marianop9/reflective-color-sensor/docs/tp_integrador_2025/presentacion/beamer.pdf

## Desarrollo de un Sensor de Colores por Reflexión

Técnicas Digitales III

Federico Beck Mariano Perez

Departamento de Ingeniería Electrónica Facultad Regional San Francisco — UTN

8 de Abril, 2026

Beck, Perez (UTN FRSF) | Sensor de Colores | 8 de Abril, 2026 | 1 / 30

## Contenidos

1 | Introducción
2 | Hardware y Diseño
3 | Circuito de Acondicionamiento
4 | Caracterización del LDR
5 | Proceso de Medición
6 | Resultados
7 | Firmware
8 | Comparación y Conclusiones
Beck, Perez (UTN FRSF) | Sensor de Colores | 8 de Abril, 2026 | 2 / 30

## Introducción y Motivación

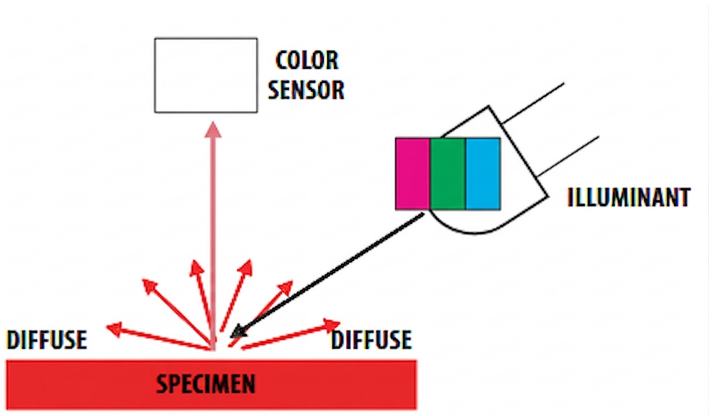
[picture p31: figure]

Objetivo: Dispositivo de bajo costo para determinación de color. Principio: Reflexión de luz roja, verde y azul sobre una superficie. Sensor: Resistencia dependiente de la luz (LDR).

Beck, Perez (UTN FRSF) | Sensor de Colores | 8 de Abril, 2026 | 3 / 30

## Opciones Comerciales

Sensor Adafruit TCS34725: utiliza luz blanca, filtros, y un fotodiodo.

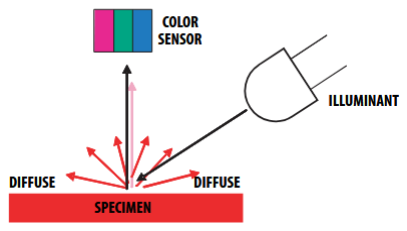
[picture p32: figure]

Figura: Sensor Adafruit TCS34725.

Beck, Perez (UTN FRSF) | Sensor de Colores | 8 de Abril, 2026 | 4 / 30

## Arquitectura del Dispositivo

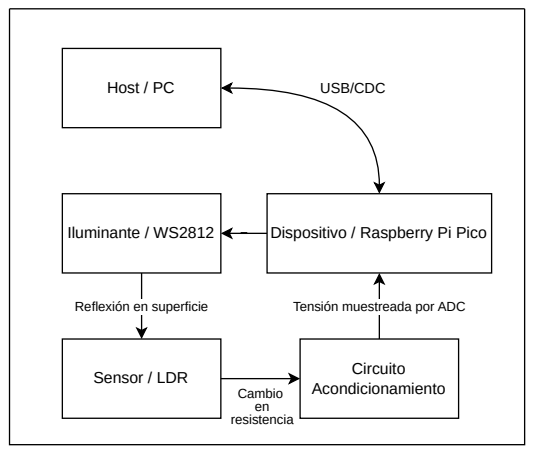
[picture p33: figure]
Host / PC; USB/CDC; Dispositivo / Raspberry Pi Pico; Reflexión en superficie; Iluminante / WS2812; Sensor / LDR; Tensión muestreada por ADC; Circuito; Cambio; Acondicionamiento; en resistencia

Beck, Perez (UTN FRSF) | Sensor de Colores | 8 de Abril, 2026 | 5 / 30

## Diseño Físico y Carcasa

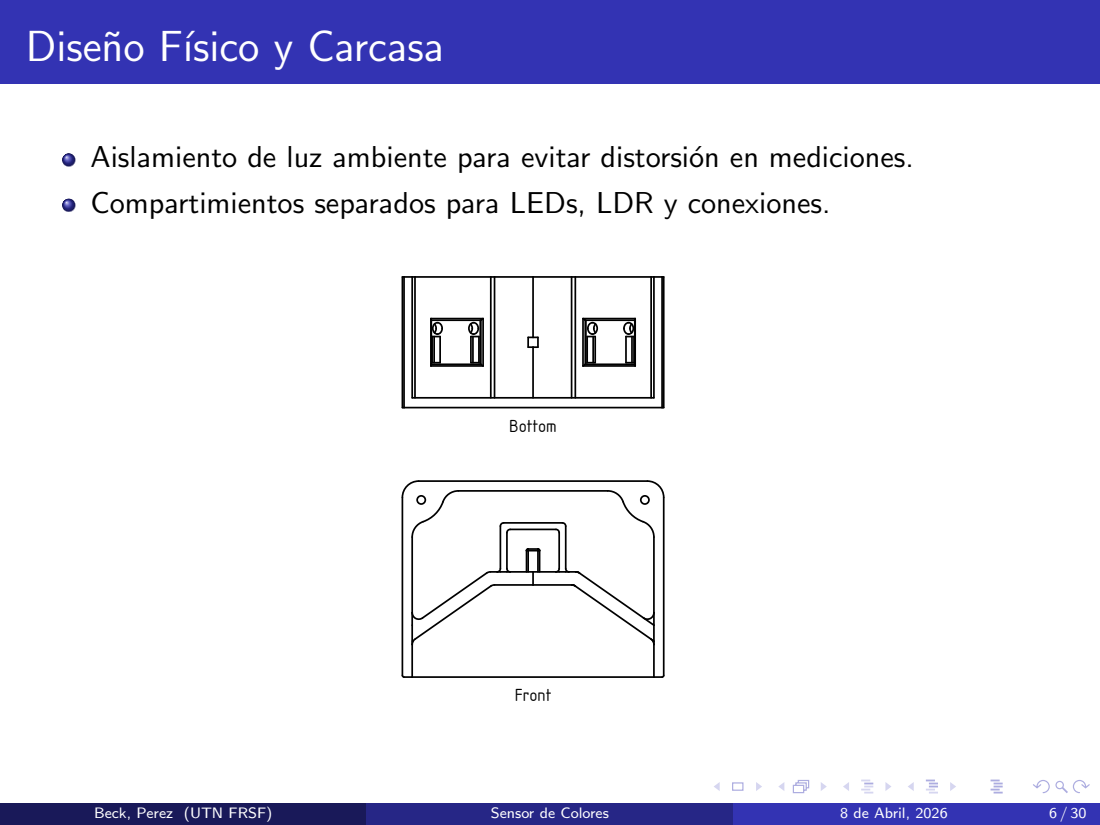
[picture p34: page 6]
Front; Bottom; Beck, Perez (UTN FRSF); Sensor de Colores; 8 de Abril, 2026

Aislamiento de luz ambiente para evitar distorsión en mediciones.
Compartimientos separados para LEDs, LDR y conexiones.

## Componentes Electrónicos: LDR


Respuesta no lineal
Distintas sensibilidades a distintas longitudes de onda.
Baja trazabilidad
Respuesta variable
La respuesta se puede aproximar como:

R = KaE

−γ

Beck, Perez (UTN FRSF) | Sensor de Colores | 8 de Abril, 2026 | 7 / 30

## Componentes Electrónicos

Unidad de Control — Raspberry Pi Pico: Microcontrolador RP2040
DMA para muestreo de ADC
Stack USB
I/O programable
Iluminantes:
LEDs WS2812 (RGB)
Múltiples LEDs conectados en cascada Circuito de Acondicionamiento: Amplificador operacional LM358 Switch cuádruple CD4066
Resistencias de 1 kΩ, 10 kΩ y 100 kΩ

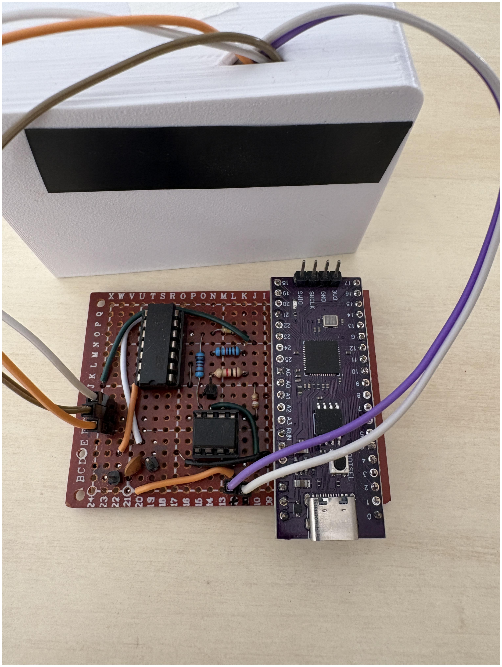
[picture p35: figure]

Beck, Perez (UTN FRSF) | Sensor de Colores | 8 de Abril, 2026 | 8 / 30

## Acondicionamiento de Señal


Vo = V+ + (V+ − Vs )

Rf

RLDR
Vo = V+ + (V+ − Vs )Rf G

Mediante el CD4066, Rf puede tomar distintos valores discretos para evitar la saturación ante el amplio rango del LDR (1 kΩ a 1000 kΩ).

Beck, Perez (UTN FRSF) | Sensor de Colores | 8 de Abril, 2026 | 9 / 30

## Respuesta del Circuito

G =

V+ − Vo
Rf ∗ (Vs − V+)


Figura: Tensión de salida vs Resistencia del LDR | para distintas Rf .
Beck, Perez (UTN FRSF) | Sensor de Colores | 8 de Abril, 2026 | 10 / 30

## Modelo Matemático del LDR

La respuesta del LDR no es lineal:

R = KE ⁻γ

E: Iluminancia
Ka, γ: Parámetros desconocidos.
Beck, Perez (UTN FRSF) | Sensor de Colores | 8 de Abril, 2026 | 11 / 30

## Modelo Matemático del LDR

La respuesta del LDR no es lineal:

R = KE ⁻γ

E: Iluminancia
Ka, γ: Parámetros desconocidos.

Expresado en terminos de conductancia:

G = KaE

γ

Beck, Perez (UTN FRSF) | Sensor de Colores | 8 de Abril, 2026 | 11 / 30

## Iluminancia

Definición

La iluminancia es la cantidad de flujo luminoso que incide sobre una superficie por unidad de área.
Define qué tan iluminada está una superficie
Medida en lux (1 lux = 1 lm/m²
)
Disminuye con el cuadrado de la distancia a la fuente Se mide con un luxómetro
Beck, Perez (UTN FRSF) | Sensor de Colores | 8 de Abril, 2026 | 12 / 30

## Modelo Matemático Aproximado del LDR


Es imposible determinar la iluminancia, por lo que se utiliza una aproximación.

E ≈ c, c ∈ [0, 255]

G = Kac

| γ
Beck, Perez (UTN FRSF) | Sensor de Colores | 8 de Abril, 2026 | 13 / 30

## Región de Funcionamiento

Se define una región de funcionamiento del dispositivo.
Para muestras del ADC con códigos por debajo de 850 y por encima de 3800, la respuesta del circuito no variaba al cambiar la intensidad de los LED.


Beck, Perez (UTN FRSF) | Sensor de Colores | 8 de Abril, 2026 | 14 / 30

## Proceso de Calibración


Cada color por separado
Barrido de intensidad
40 valores de intensidad
Espaciado logarítmico
Si la medición no se encuentra dentro de la región de funcionamiento, se ajusta la resistencia de ganancia y se repite.
Beck, Perez (UTN FRSF) | Sensor de Colores | 8 de Abril, 2026 | 15 / 30

## Proceso de Calibración

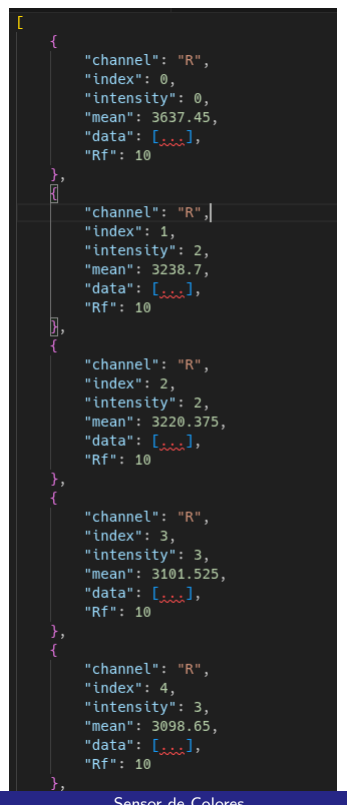
[picture p36: figure]

Beck, Perez (UTN FRSF) | Sensor de Colores | 8 de Abril, 2026 | 16 / 30

## Proceso de Calibración


Beck, Perez (UTN FRSF) | Sensor de Colores | 8 de Abril, 2026 | 16 / 30

## Cálculo de los Parametros del LDR

Una vez recolectadas las muestras para cada color, se aplica la técnica de mínimos cuadrados (LSQ) para aproximar la respuesta.
La i-ésima muestra recolectada se expresa como:

Gi = Kac

γ
i
Beck, Perez (UTN FRSF) | Sensor de Colores | 8 de Abril, 2026 | 17 / 30

## Cálculo de los Parametros del LDR

Una vez recolectadas las muestras para cada color, se aplica la técnica de mínimos cuadrados (LSQ) para aproximar la respuesta.
La i-ésima muestra recolectada se expresa como:

Gi = Kac

γ
i
ln Gi = lnKa + γ ln c | (1)
Beck, Perez (UTN FRSF) | Sensor de Colores | 8 de Abril, 2026 | 17 / 30

## Cálculo de los Parametros del LDR

Una vez recolectadas las muestras para cada color, se aplica la técnica de mínimos cuadrados (LSQ) para aproximar la respuesta.
La i-ésima muestra recolectada se expresa como:

Gi = Kac

γ
i
ln Gi = lnKa + γ ln c | (1)

Considerando N muestras distintas, se arma un sistema de ecuaciones y se expresa en forma de matrices:

ln G1
ln G2
ln GN

=

1 | ln c1
1 | ln c2
1 ln cN

lnKa
γ
(2)
Beck, Perez (UTN FRSF) | Sensor de Colores | 8 de Abril, 2026 | 17 / 30

## Cálculo de los Parámetros del LDR

Considerando N muestras distintas, se arma un sistema de ecuaciones y se expresa en forma de matrices:

ln G1
ln G2
ln GN

=

1 | ln c1
1 | ln c2

1 ln cN

lnKa
γ

Y = Ax

Los valores de la matriz x que mejor se ajustan a las muestras obtenidas se puede calcular como:
x = (A

T A)

−1
A
T Y | (3)
Beck, Perez (UTN FRSF) | Sensor de Colores | 8 de Abril, 2026 | 18 / 30

## Parámetros del LDR

{
"R": {
"Ka": 0.011508412425650682 , " gamma ": 0.8527065806062964 },
"G": {
"Ka": 0.0032507832523976554 , " gamma ": 0.8597395131749697 },
"B": {
"Ka": 0.0030240133142661603 , " gamma ": 0.8283233614433873 }
}
Beck, Perez (UTN FRSF) | Sensor de Colores | 8 de Abril, 2026 | 19 / 30

## Proceso de Medición

Una vez determinados los parámetros del LDR, se pueden tomar mediciones. Para cada color R-G-B:
1 | Se coloca el dispositivo sobre la superficie a medir.
2 | Iluminación a máxima intensidad.
3 | Muestreo de tensión y cálculo de G.
| G ≈ Kac γ
| G se mide
| Ka, γ se conocen de la calibración
Beck, Perez (UTN FRSF) | Sensor de Colores | 8 de Abril, 2026 | 20 / 30

## Resultados

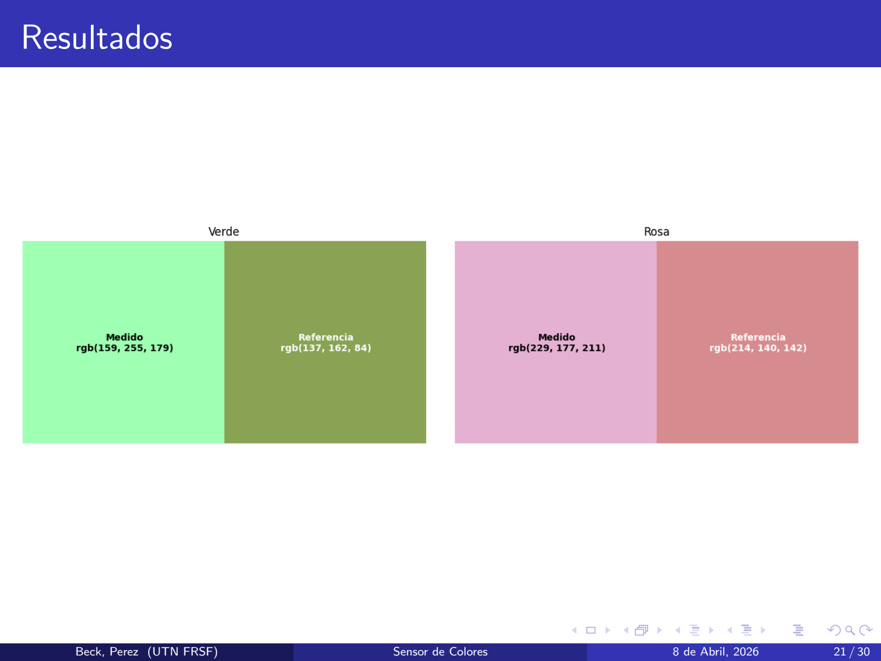
[picture p37: page 25]

Beck, Perez (UTN FRSF) | Sensor de Colores | 8 de Abril, 2026 | 21 / 30

## Resultados

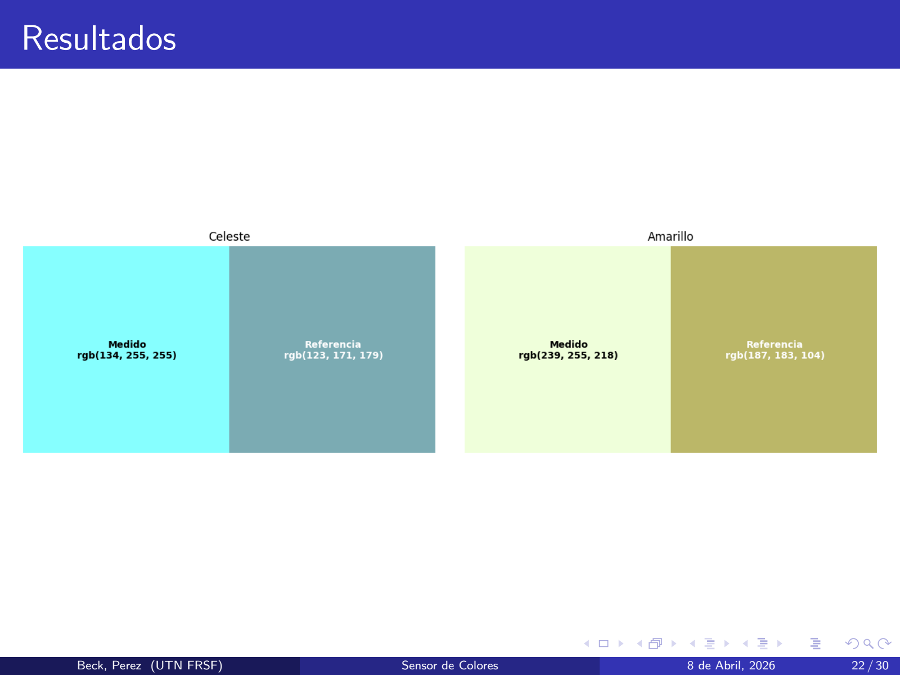
[picture p38: page 26]

Beck, Perez (UTN FRSF) | Sensor de Colores | 8 de Abril, 2026 | 22 / 30

## Implementación en Firmware

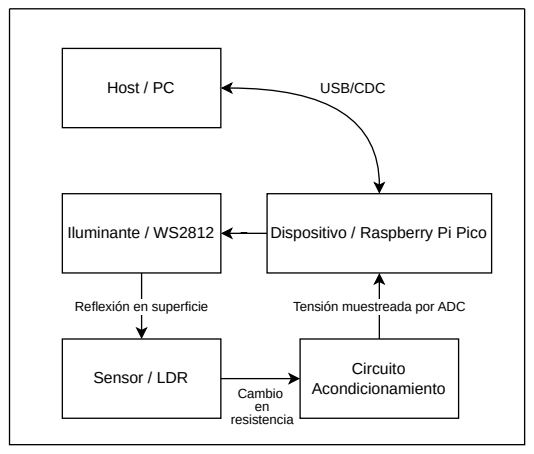
[picture p39: figure]
Host / PC; USB/CDC; Dispositivo / Raspberry Pi Pico; Reflexión en superficie; Iluminante / WS2812; Sensor / LDR; Tensión muestreada por ADC; Circuito; Cambio; Acondicionamiento; en resistencia

Beck, Perez (UTN FRSF) | Sensor de Colores | 8 de Abril, 2026 | 23 / 30

## Arquitectura del Firmware

Implementación en C
Abstracción de hardware: Pico-SDK Implementación del stack USB: TinyUSB SO de tiempo real: FreeRTOS
Beck, Perez (UTN FRSF) | Sensor de Colores | 8 de Abril, 2026 | 24 / 30

## Arquitectura del Firmware

usb task()
Ejecuta del stack USB
Recibe/envía de mensajes desde/hacía el host worker task()
Ejecuta de comandos
Interactúa con periféricos a través de drivers Arma de mensajes de respuesta
Librería ascii-communication-protocol (ACP)

Interpreta mensajes recibidos como comandos Codifica mensajes a enviar en el formato de respuesta

Beck, Perez (UTN FRSF) | Sensor de Colores | 8 de Abril, 2026 | 25 / 30

## Arquitectura del Firmware

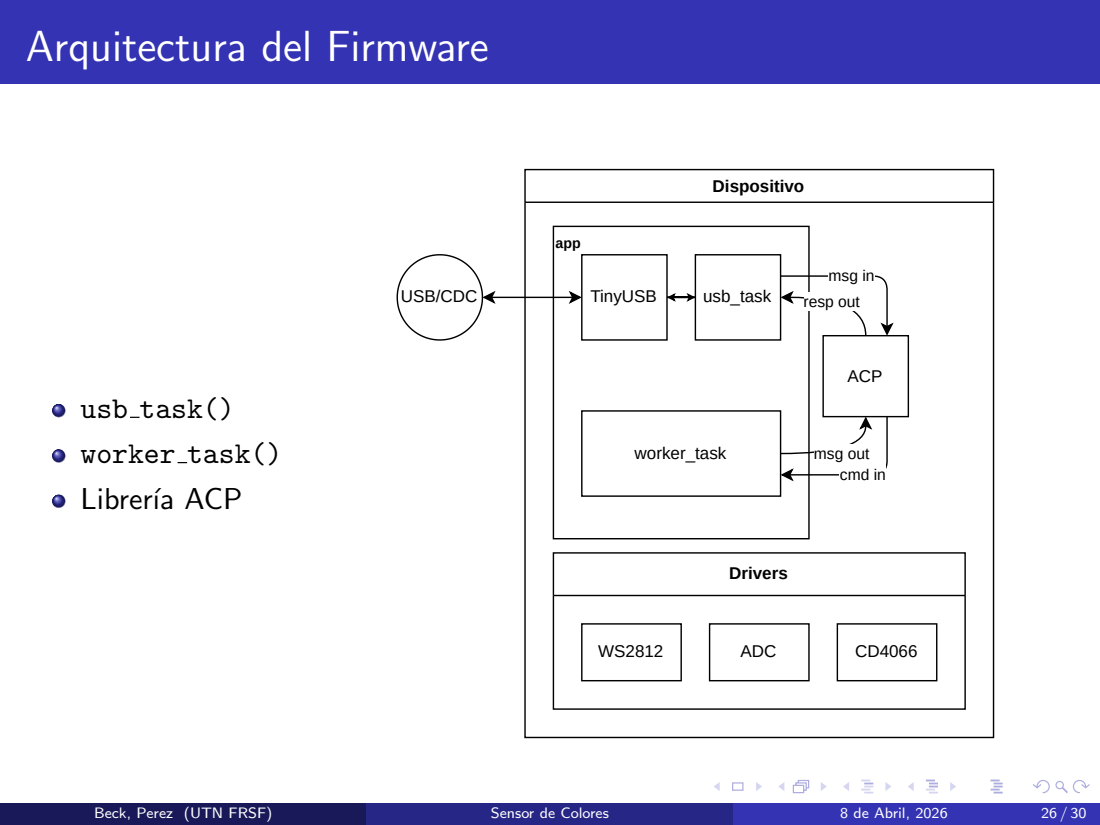
[picture p40: page 30]
Dispositivo; app; msg in; usb_task; worker_task; msg out; cmd in; ACP; Drivers; ADC; resp out USB/CDC; inyUSB; Beck, Perez (UTN FRSF); Sensor de Colores; 8 de Abril, 2026

usb task()
worker task()
Librería ACP

## Aplicación CLI

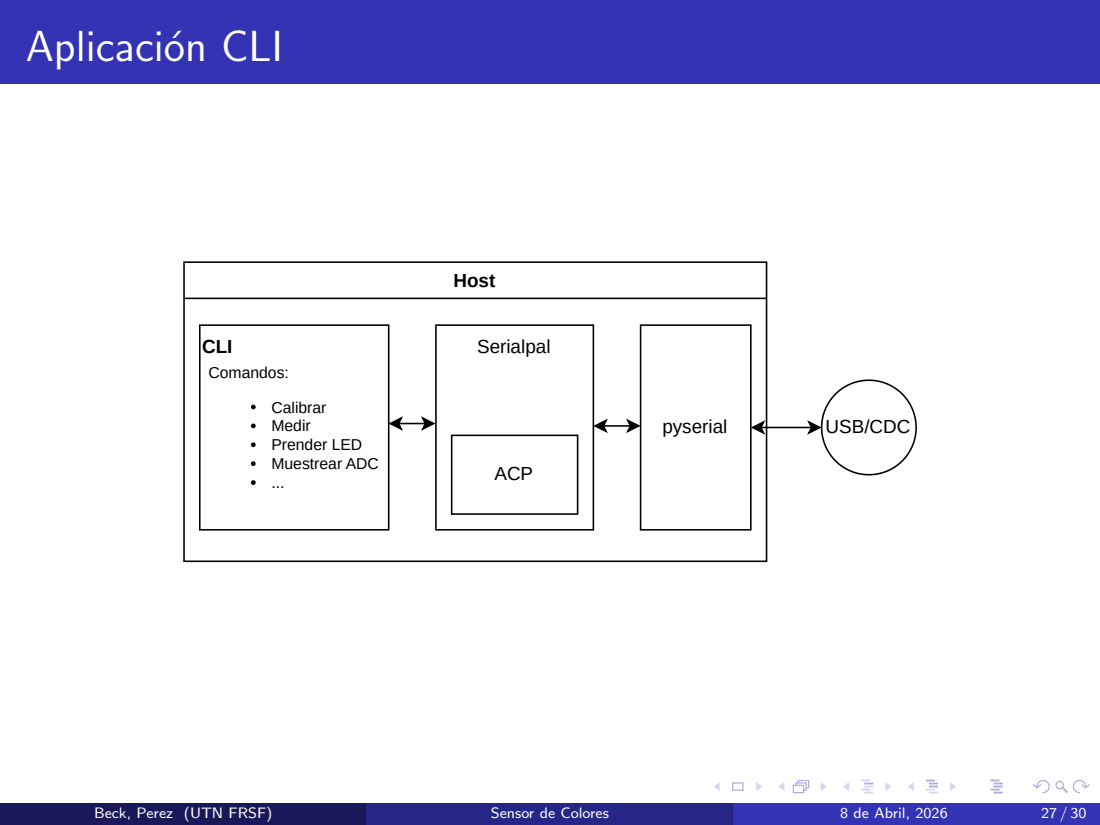
[picture p41: page 31]
Host; pyserial; CLI; Serialpal; Comandos:; ACP; USB/CDC; Beck, Perez (UTN FRSF); Sensor de Colores; 8 de Abril, 2026

Calibrar
Medir
Prender LED Muestrear ADC

## Compración con la Versión Inicial

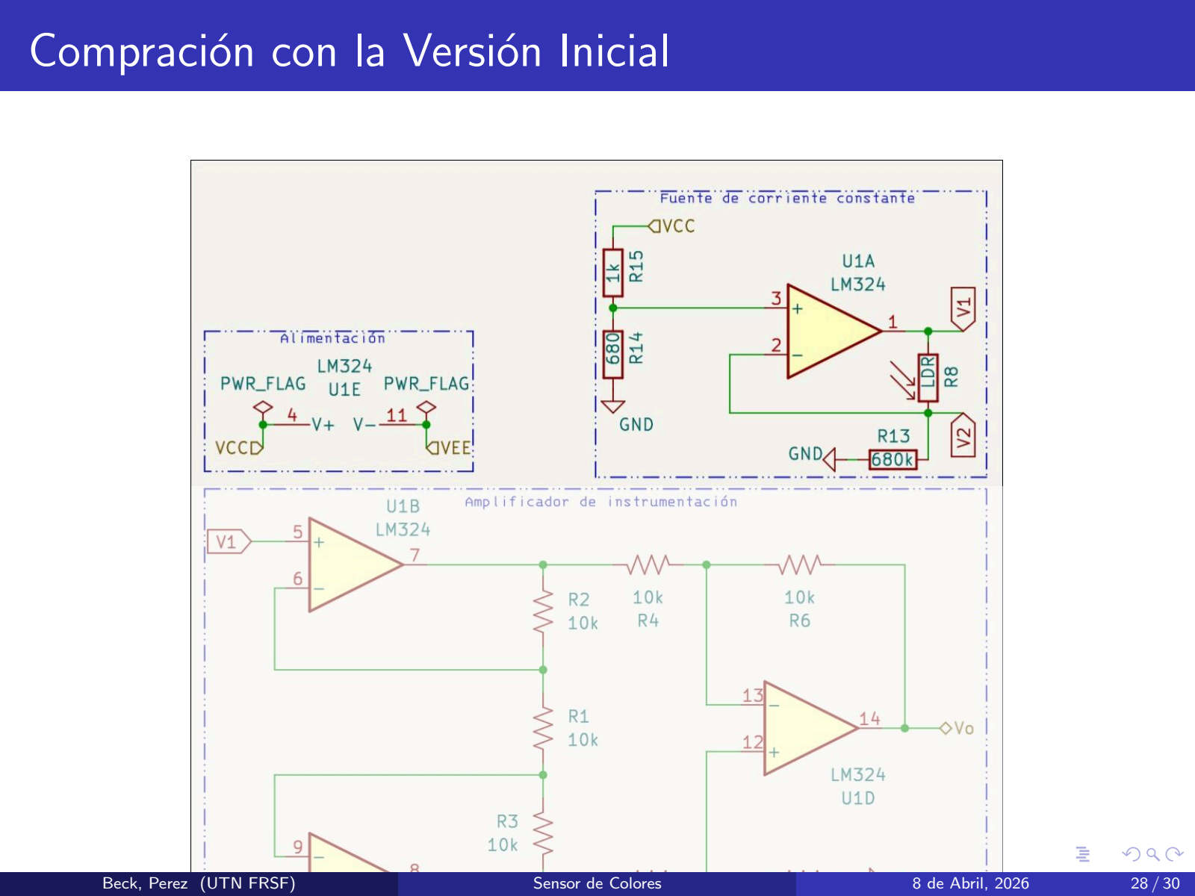
[picture p42: page 32]

Beck, | Perez | (UTN FRSF) | Sensor de Colores | 8 de Abril, 2026 | 28 / 30

## Compración con la Versión Inicial

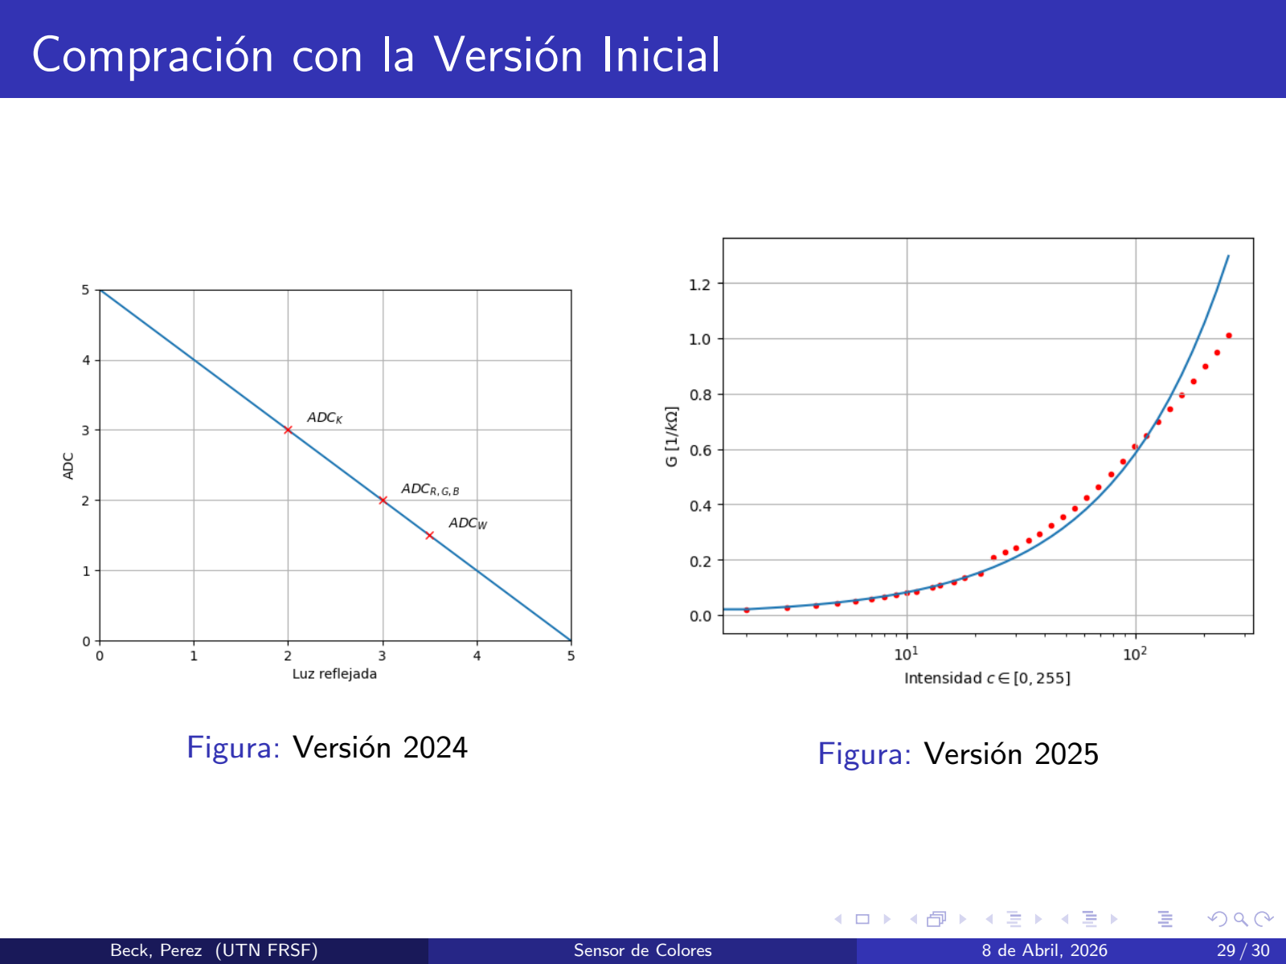
[picture p43: page 33]

Figura: Versión 2024 | Figura: Versión 2025
Beck, Perez (UTN FRSF) | Sensor de Colores | 8 de Abril, 2026 | 29 / 30

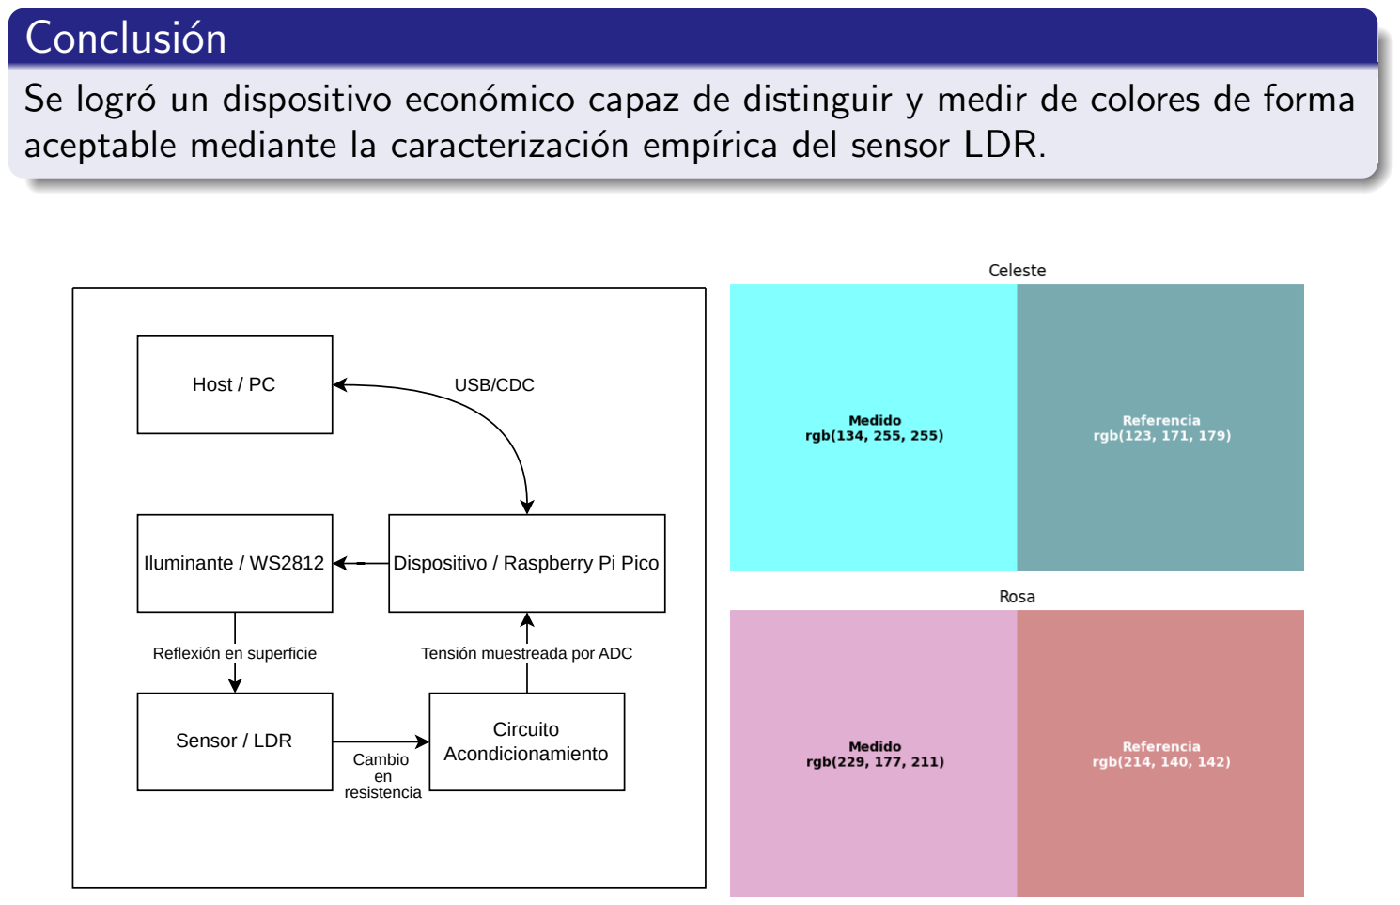
[picture p44: figure]
Conclusión; Dispositivo / Raspberry Pi Pico; Reflexión en superficie; Iluminante / WS2812; Sensor / LDR; Tensión muestreada por ADC; Circuito; Cambio; Acondicionamiento; en resistencia

Se logró un dispositivo económico capaz de distinguir y medir de colores de forma
aceptable mediante la caracterización empírica del sensor LDR. Host / PC | USB/CDC
Beck, Perez (UTN FRSF) | Sensor de Colores | 8 de Abril, 2026 | 30 / 30
