marianop9/reflective-color-sensor/docs/tp_integrador_2025/img/beamer/final_slide.pdf

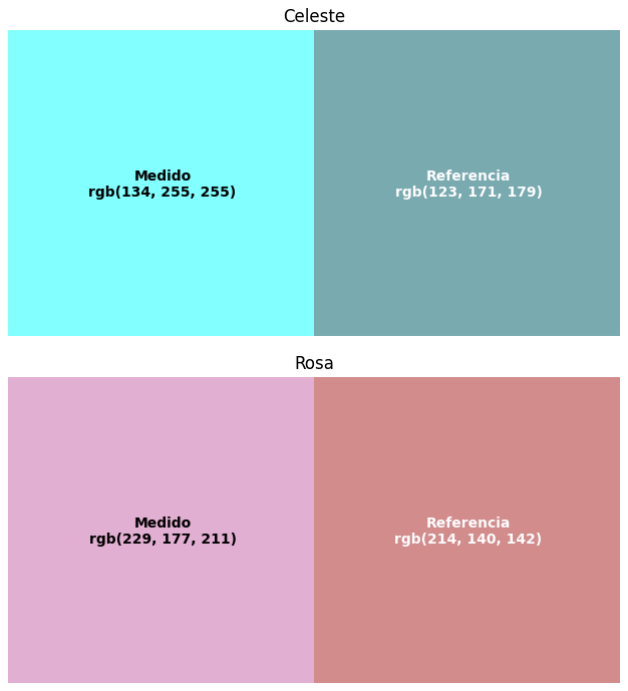
[picture p45: figure]
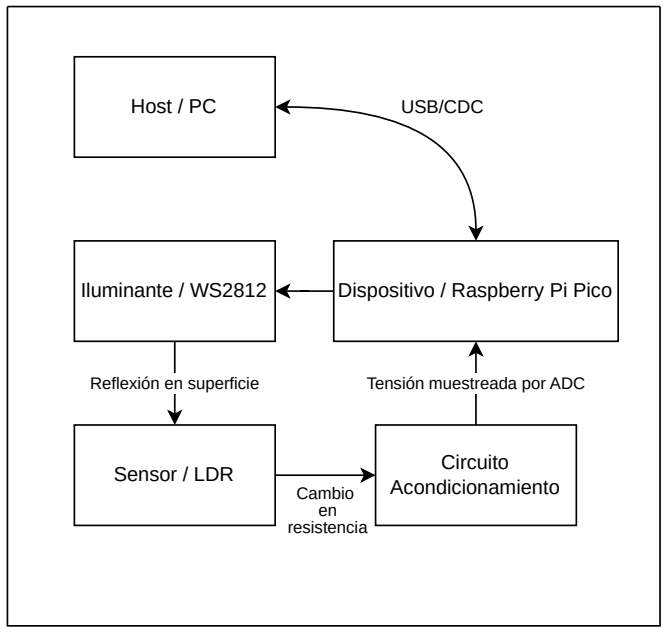
[picture p46: figure]
Host / PC; USB/CDC; Dispositivo / Raspberry Pi Pico; Reflexión en superficie; Iluminante / WS2812; Sensor / LDR; Tensión muestreada por ADC; Circuito; Cambio; Acondicionamiento; en resistencia
