marianop9/reflective-color-sensor/docs/tp_integrador_2025/img/beamer/circuito_2024.pdf

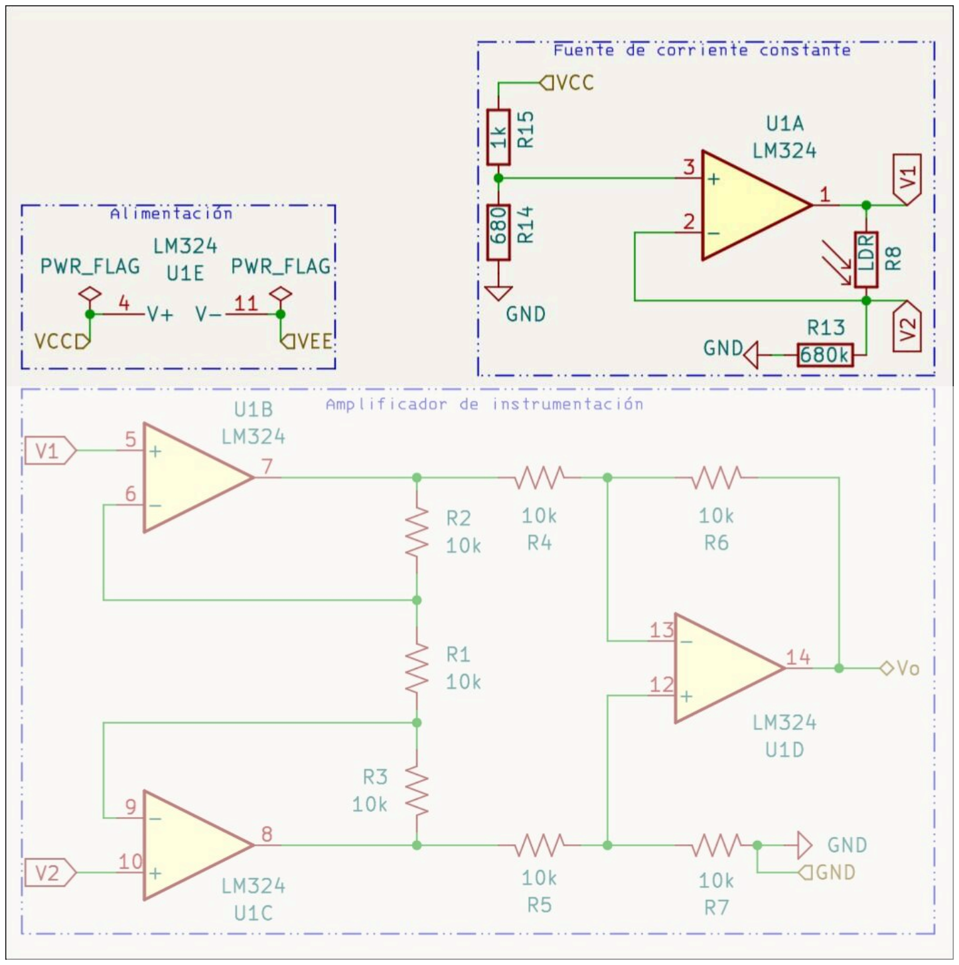
[picture p47: page 1]
