marianop9/reflective-color-sensor/docs/tp_integrador_2025/img/diagrama_inicial.png

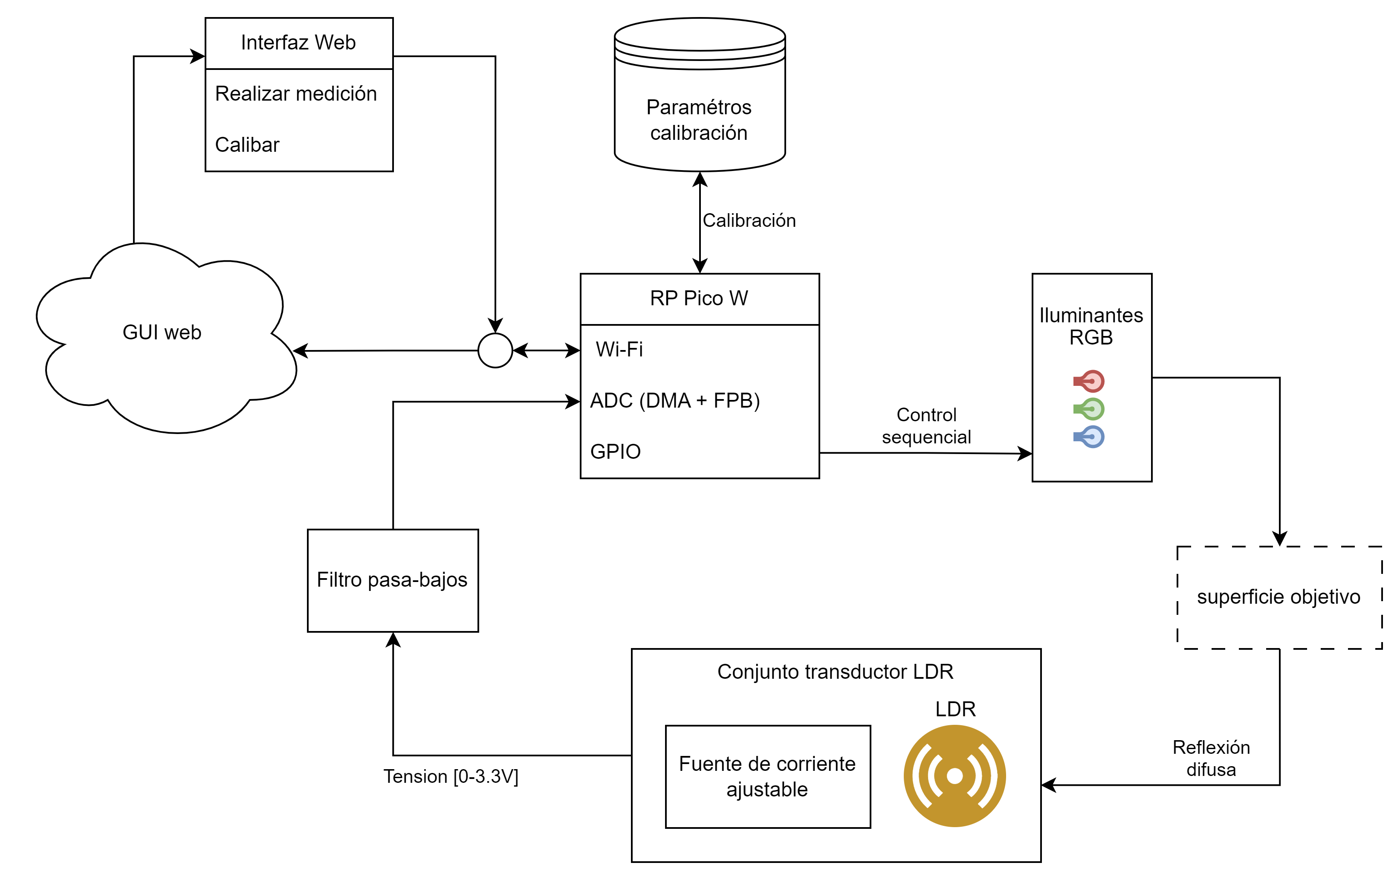
docs/tp_integrador_2025/img/diagrama_inicial.png
