marianop9/reflective-color-sensor/scripts/filtrado_043V.png

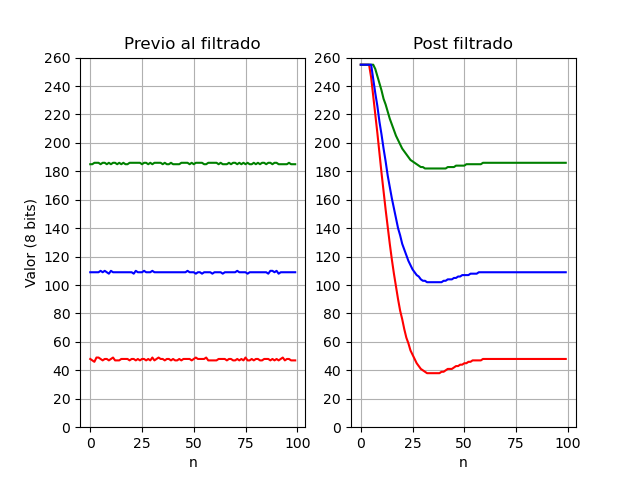
scripts/filtrado_043V.png
