marianop9/reflective-color-sensor/scripts/sin_filtro_043V.png

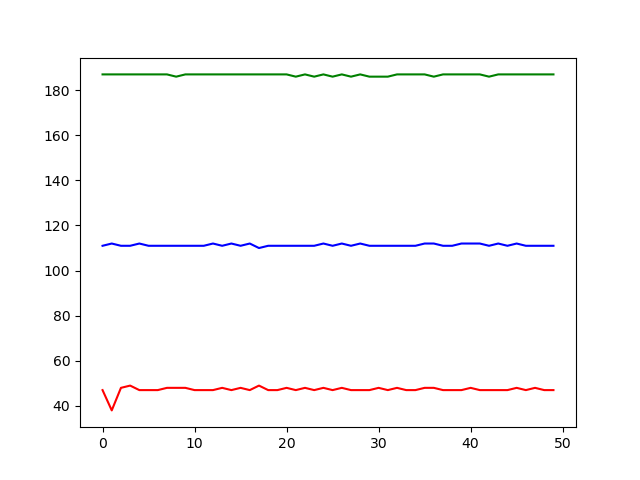
scripts/sin_filtro_043V.png
