marianop9/reflective-color-sensor/circuitos/ldr_conditioning_v2_sim/ldr_conditioning.asc

R1: res; {LDR}
R2: res; {Rf}
R3: res; 1.2k
R4: res; 2.2k
U2: opamp
V1: voltage; 5
Named nets: 0, Vdiv, Vo
.lib opamp.sub
.op
.step dec param LDR 1k 1MEg 10
.step param Rf list 1k 10k 100k 500k
