marianop9/reflective-color-sensor/scripts/serialpal/serialpal/serialpal.py

import serial
import serial.tools.list_ports
from typing import Literal
import struct


FORMAT_SPECIFIERS_BY_BITS = {8: "B", 16: "H"}


class Response:
    def __init__(self, type: Literal["ERR", "TEXT", "DATA"],
                 raw_payload: bytes,
                 #  data: str | tuple[int],
                 len_bytes):
        self.type = type
        self.raw_payload = raw_payload
        self.payload_len_bytes = len_bytes
        self.payload = None

    def is_error(self):
        return self.type == "ERR"

    def decode(self, *, data_size=16) -> bool:
        if self.payload is not None:
            return True

        if self.type not in ["ERR", "TEXT", "DATA"]:
            print("unknown response type: ", self.type)
            return False

        if self.type in ["ERR", "TEXT"]:
            self.payload = self.raw_payload.decode("ascii")
        elif self.type == "DATA":
            format_spec = FORMAT_SPECIFIERS_BY_BITS.get(data_size)
            if format_spec is None:
                print('unsupported data size: ', data_size)
                return False

            payload_len = int(self.payload_len_bytes*8/data_size)
            self.payload = struct.unpack(
                f"<{payload_len}{format_spec}", self.raw_payload)

        return True

    def format(self):
        if self.payload is None:
            return ""

        return "{} ({}): {}".format(self.type,
                                    self.payload_len_bytes,
                                    self.payload)


_port_settings = dict(
    baudrate=9600,
    parity=serial.PARITY_NONE,
    stopbits=serial.STOPBITS_ONE,
    bytesize=serial.EIGHTBITS,
    timeout=5,
)


class SerialPal():
    def __init__(self, port_settings=_port_settings):
        self.serial_port = serial.Serial(port=None, **port_settings)
        self._port_list = None

    @property
    def port_list(self):
        "List available ports"
        if self._port_list is None:
            self._port_list = serial.tools.list_ports.comports()

        return self._port_list

    def serial_port_name(self):
        return self.serial_port.port

    def is_serial_port_open(self):
        return self.serial_port.is_open

    def close(self):
        self.serial_port.close()

    def connect(self, port: str) -> bool:
        """Connect to a specific port by index (must call `ports` first)

        Alternatively, provide the full port name (e.g., COMx)
        """
        port = port.strip()
        if port == "":
            return

        if port.isdigit():
            if len(self._port_list) == 0:
                print("no scanned ports")
                return

            self.serial_port.port = self._port_list[int(port)].device
        else:
            self.serial_port.port = port

        try:
            self.serial_port.open()
        except serial.SerialException as e:
            print("failed to open port: ", e)
            return False

        print(f"{self.serial_port.port} open!")
        return True

    def receive(self) -> Response | None:
        if not self.serial_port.is_open:
            print("no open ports")
            return None

        recv = self.serial_port.read_until(b";", 12)
        header = recv.decode("ascii")

        if not header.startswith("&"):
            print(f"RECV failed: unknwon resp (no startchar): {header}")
            return None

        parts = header[1:-1].split(",")
        if len(parts) != 2:
            print(f"RECV failed: unknwon resp (invalid header): {header}")
            return None

        resp_type = parts[0]
        payload_len_bytes = int(parts[1])

        raw_payload = self.serial_port.read(payload_len_bytes)
        if len(raw_payload) == 0:
            print(f"RECV failed: received no payload for: {header}")
            return None

        if len(raw_payload) != payload_len_bytes:
            print(
                f"RECV failed: incompl. payload ({len(raw_payload)}/{payload_len_bytes})")
            return None

        resp = Response(resp_type, raw_payload, payload_len_bytes)

        return resp

    def send(self, cmd: str, arg1="", arg2=""):
        if not self.serial_port.is_open:
            print("no open ports")
            return

        cmd_fmt = "&{},{},{}*"
        out: bytes
        try:
            out = cmd_fmt.format(cmd, arg1, arg2).encode("ascii")
            print(out)
        except UnicodeEncodeError:
            print("command can't be ASCII-encoded")
            return

        n = self.serial_port.write(out)
        status = "OK" if n == len(out) else "ERR"
        print(f"{status} ({n})")
