marianop9/reflective-color-sensor/docs/tp_integrador_2025/img/medicion_resultados_comprim.JPG

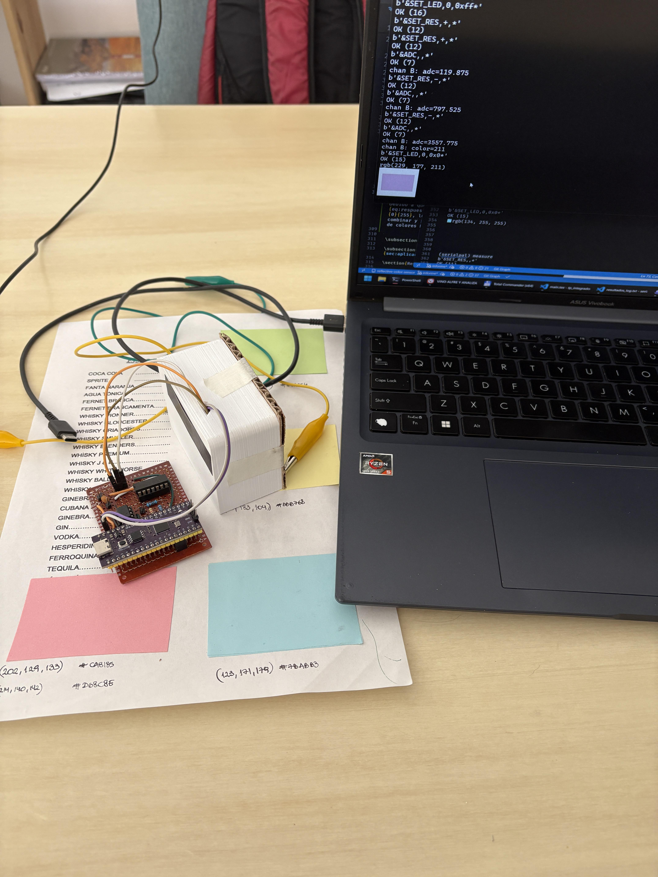
docs/tp_integrador_2025/img/medicion_resultados_comprim.JPG
